Jozko-Mrkvicka/Computer/Docs/CharTable_7x5_Example.png

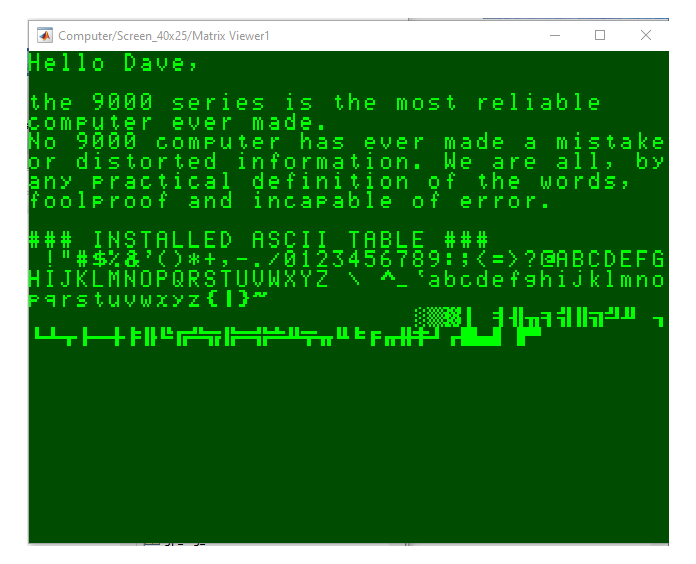
Docs/CharTable_7x5_Example.png
